n19k6/squarewave/v01_1000_rpm/oscilloscope_1.png

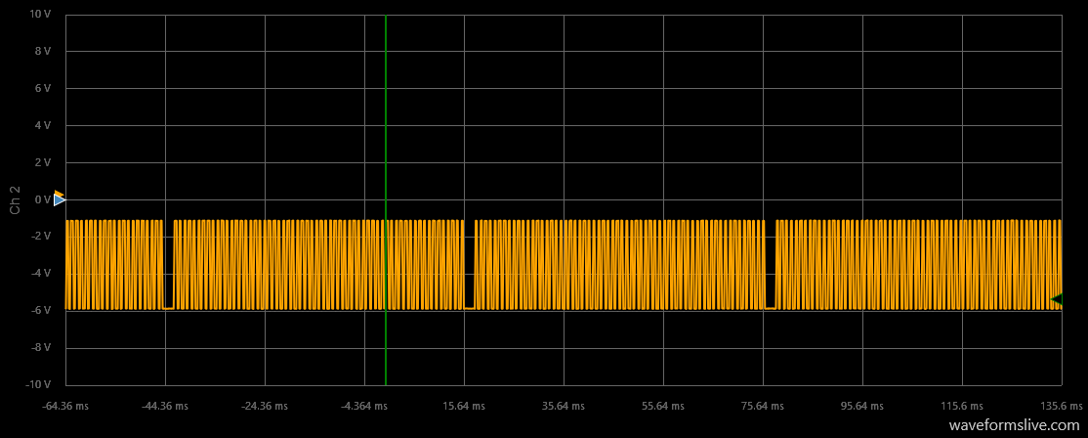
v01_1000_rpm/oscilloscope_1.png
