n19k6/squarewave/v02_maximum/az-logic-analyzer.jpg

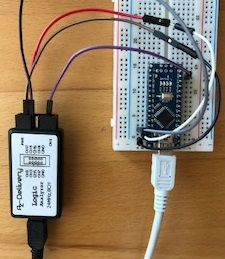
v02_maximum/az-logic-analyzer.jpg
