n19k6/squarewave/v02_maximum/signal.png

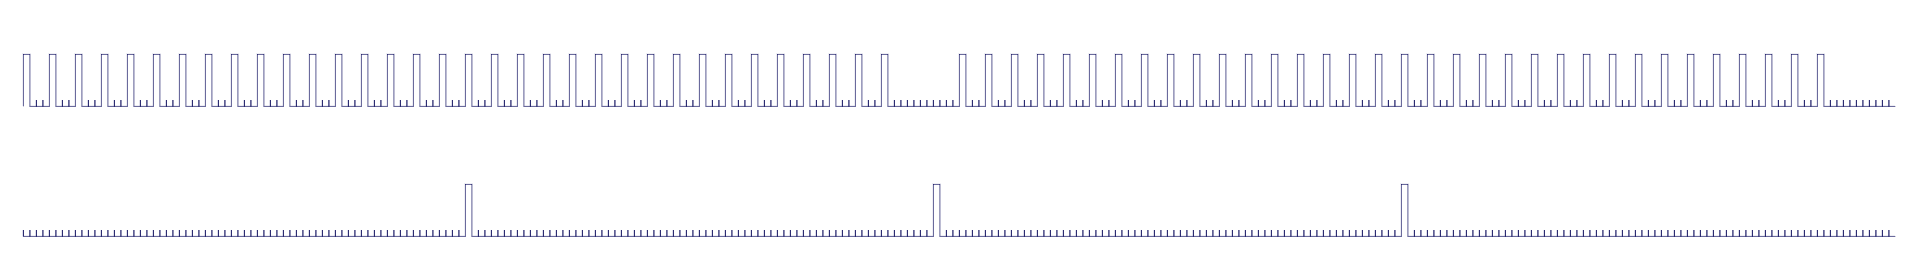
v02_maximum/signal.png
