n19k6/squarewave/v02_maximum/wave1.png

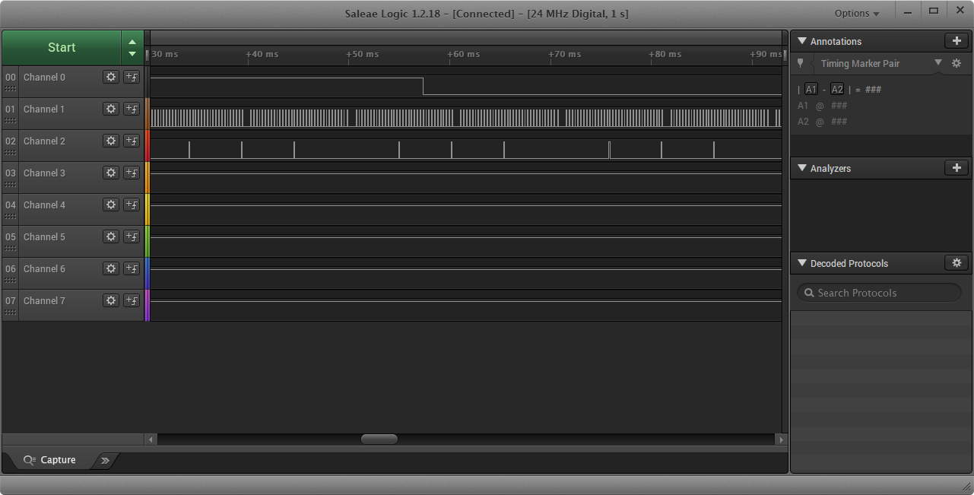
v02_maximum/wave1.png
