n19k6/squarewave/v02_maximum/wave2.png

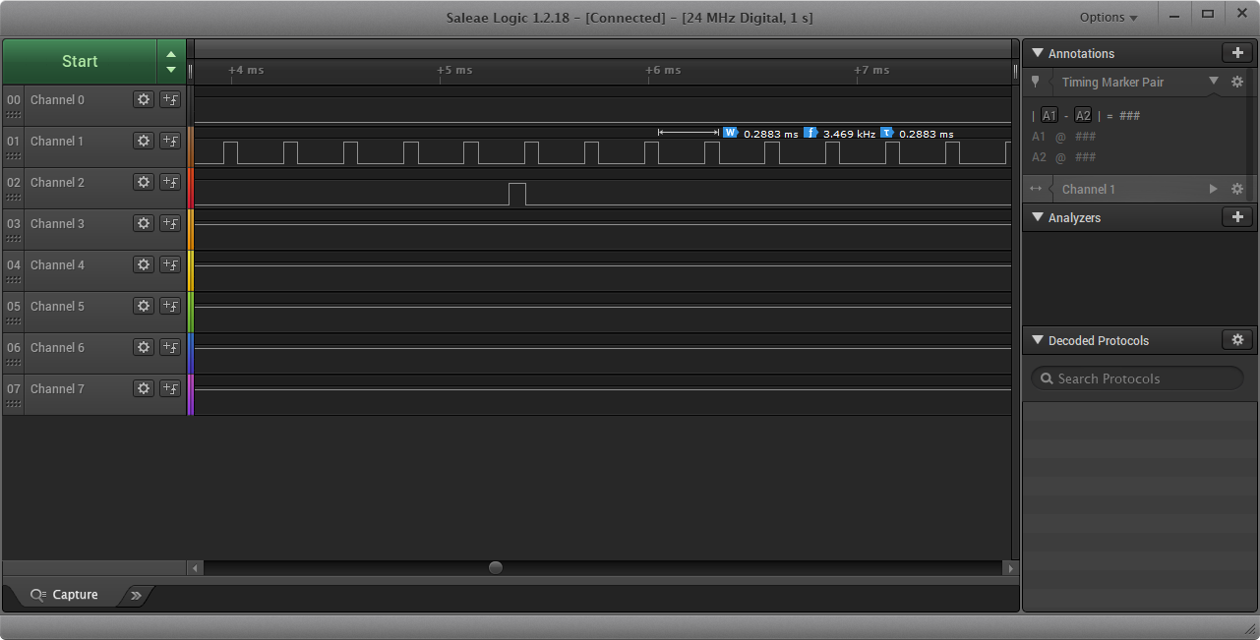
v02_maximum/wave2.png
