n19k6/squarewave/v04_sg/sketch_20210123a.png

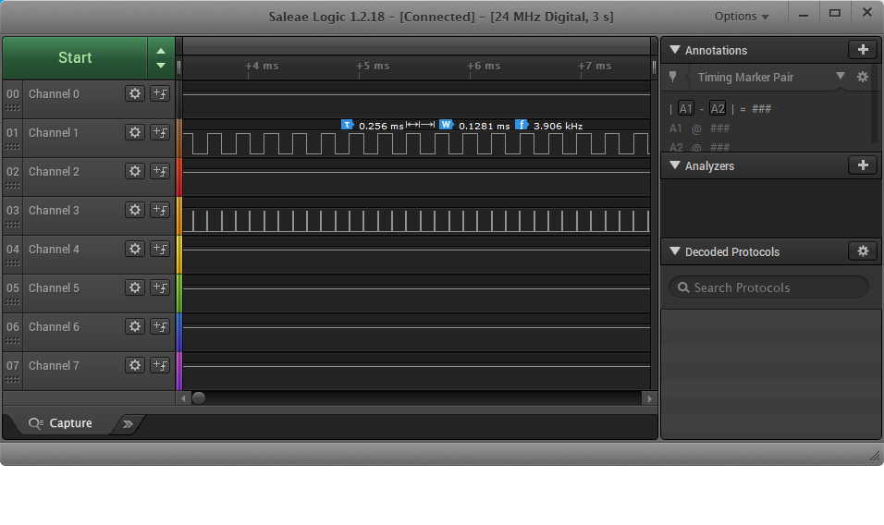
v04_sg/sketch_20210123a.png
