n19k6/squarewave/v04_sg/sketch_20210123d_100.png

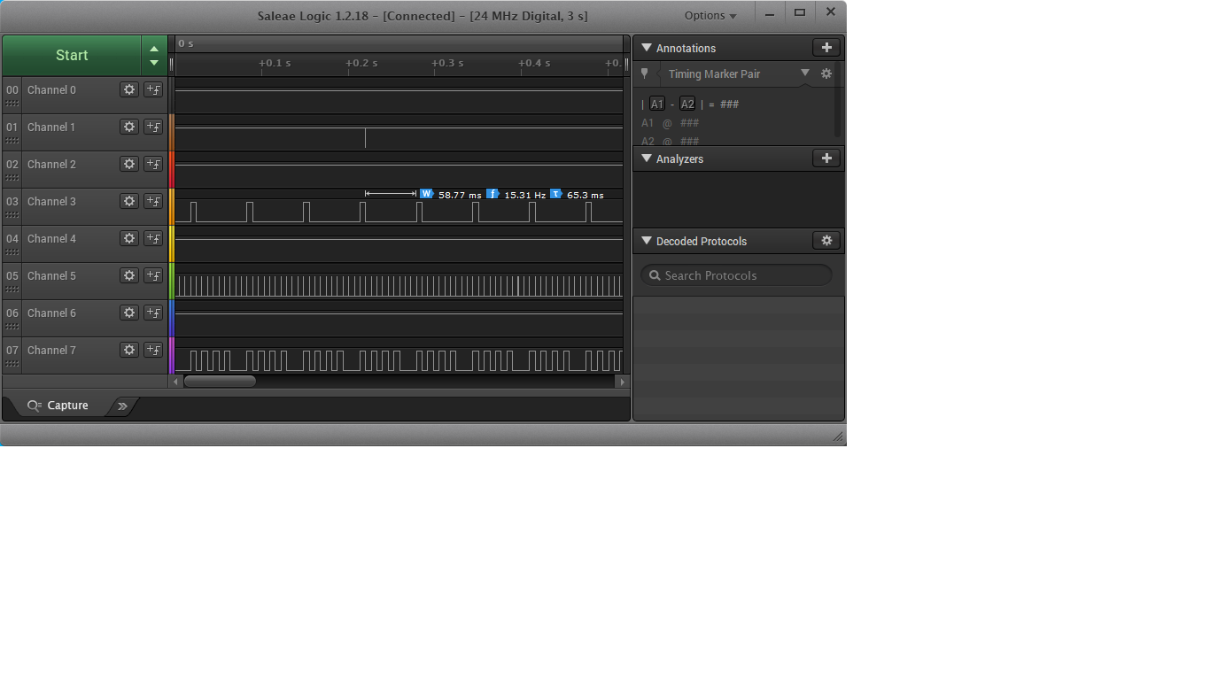
v04_sg/sketch_20210123d_100.png
