n19k6/squarewave/v04_sg/sketch_20210123f.png

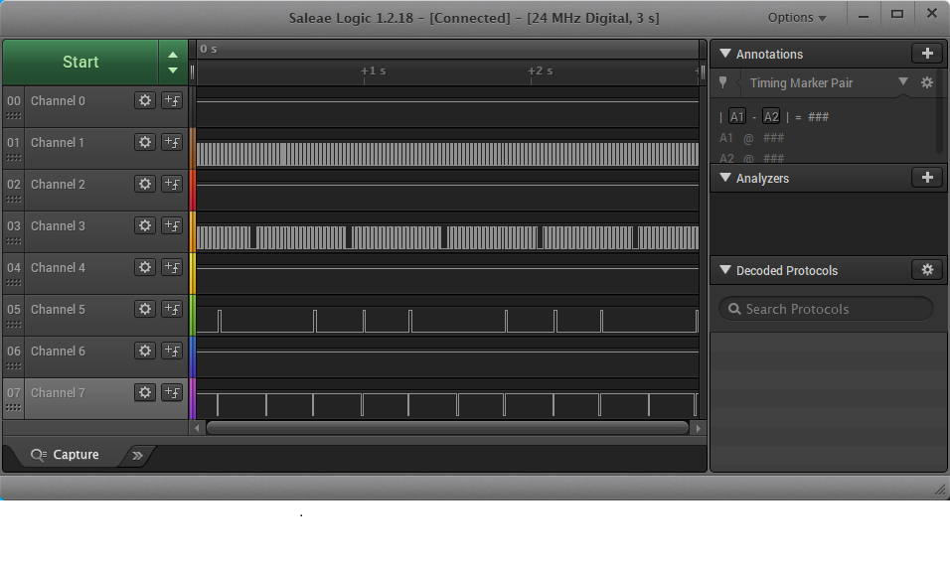
v04_sg/sketch_20210123f.png
