n19k6/squarewave/v04_sg/sketch_20210123g.png

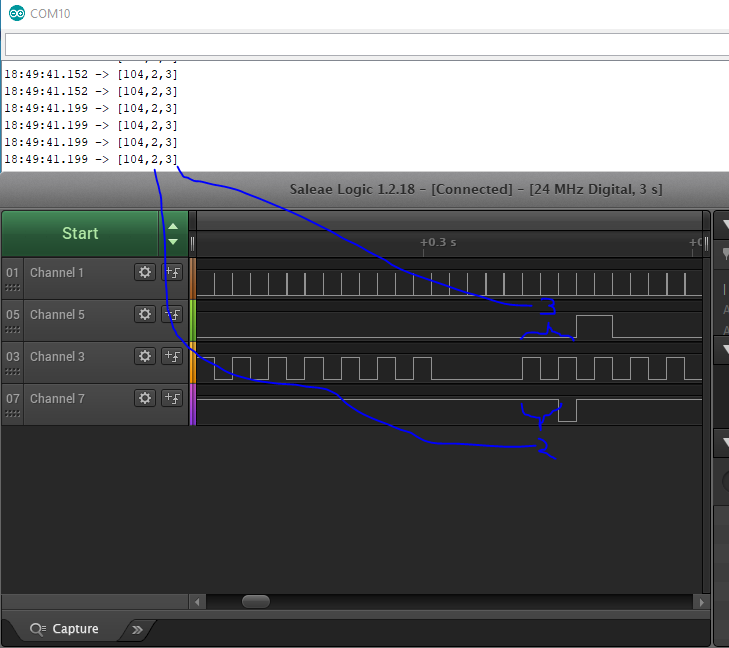
v04_sg/sketch_20210123g.png
