n19k6/squarewave/v04_sg/sketch_20210208a_timer2.png

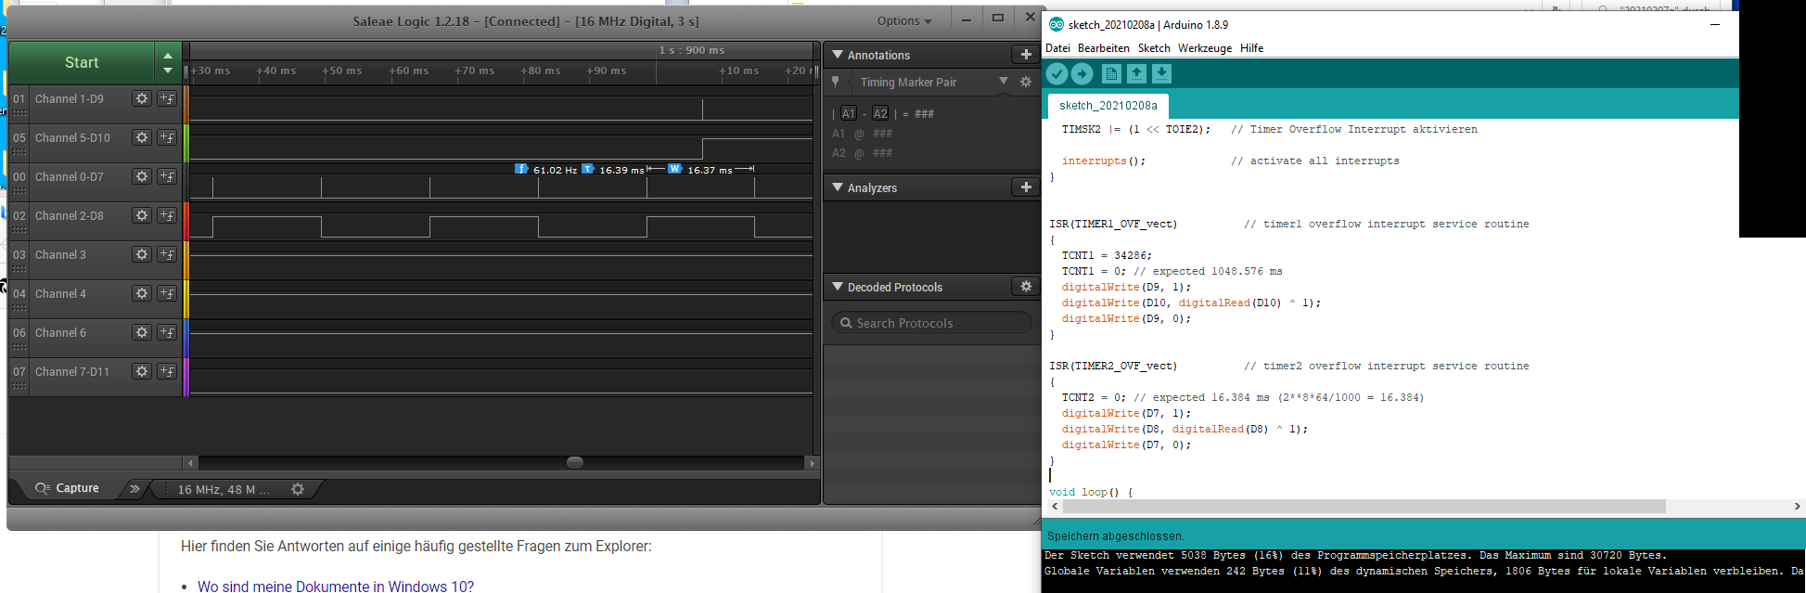
v04_sg/sketch_20210208a_timer2.png
