n19k6/squarewave/v04_sg/sketch_20210214b2.png

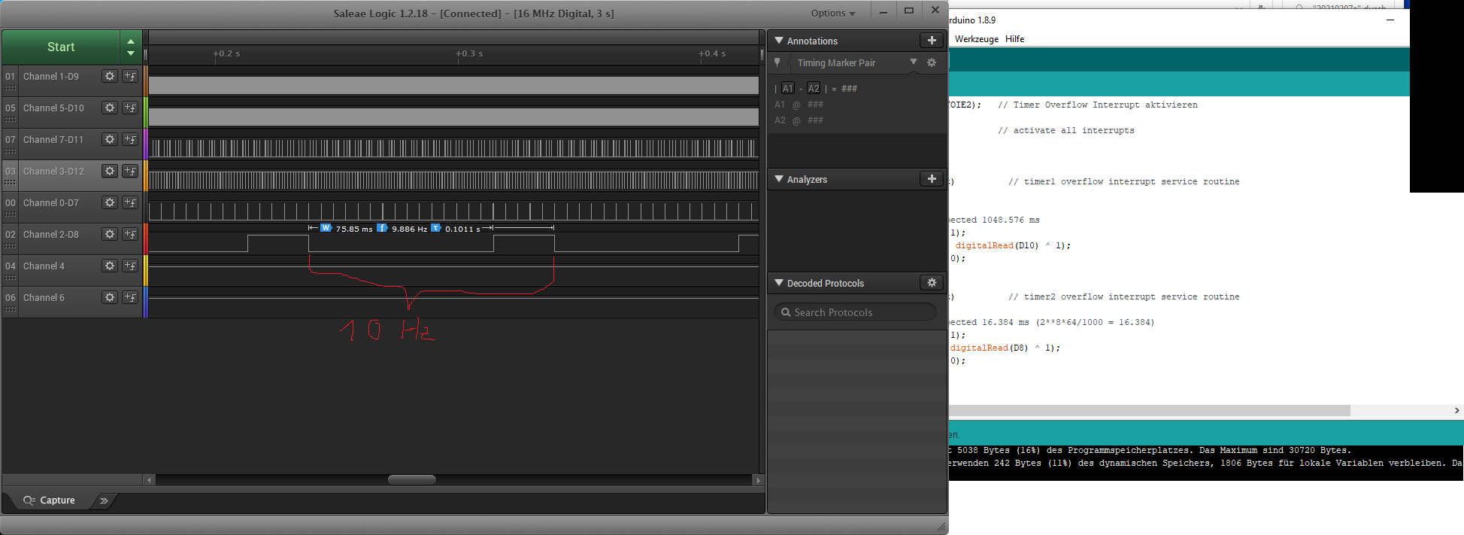
v04_sg/sketch_20210214b2.png
