n19k6/squarewave/v08_prototype_version_1/Pico_MCP3008_Schaltplan.png

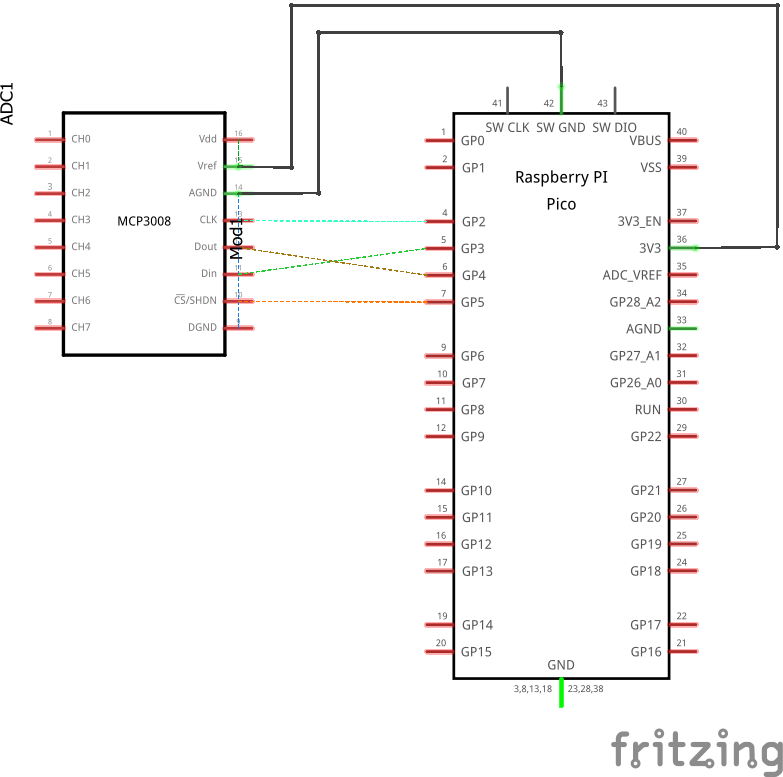
v08_prototype_version_1/Pico_MCP3008_Schaltplan.png
