n19k6/squarewave/v10_prototype_version_2/20220103/20210521_wegfahrsperre_002.png

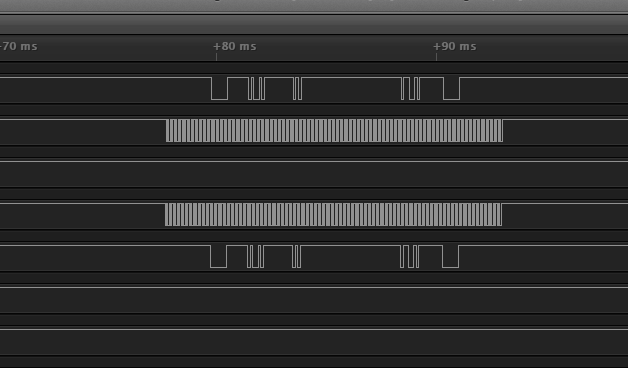
v10_prototype_version_2/20220103/20210521_wegfahrsperre_002.png
