n19k6/squarewave/v10_prototype_version_2/20220103/20220104_drei_signale_002a_freq_400_000.png

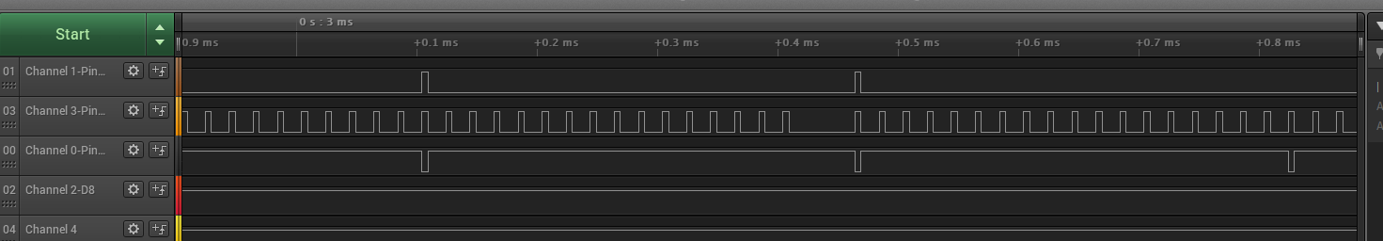
v10_prototype_version_2/20220103/20220104_drei_signale_002a_freq_400_000.png
