n19k6/squarewave/v10_prototype_version_2/20220103/20220104_drei_signale_003.png

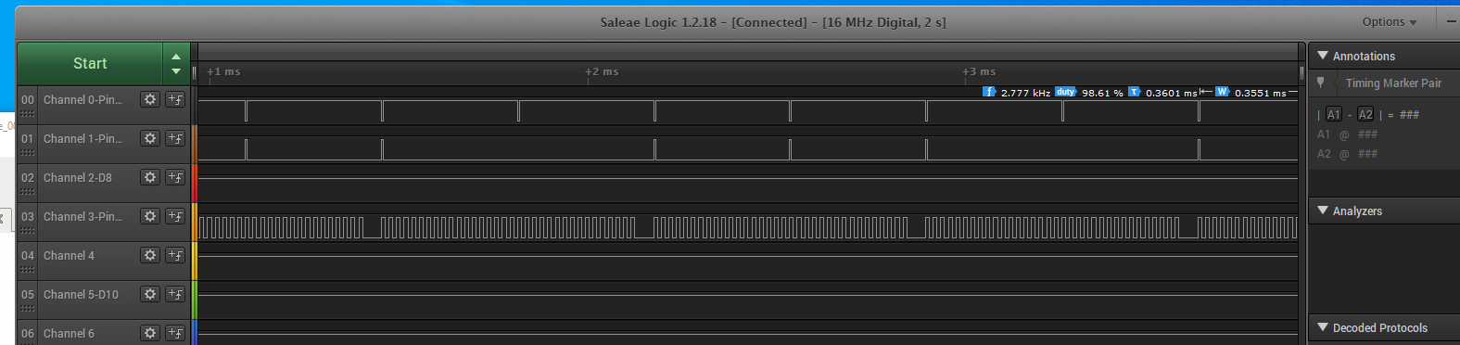
v10_prototype_version_2/20220103/20220104_drei_signale_003.png
