n19k6/squarewave/v11_honda_v1/01_input_docs/signal.png

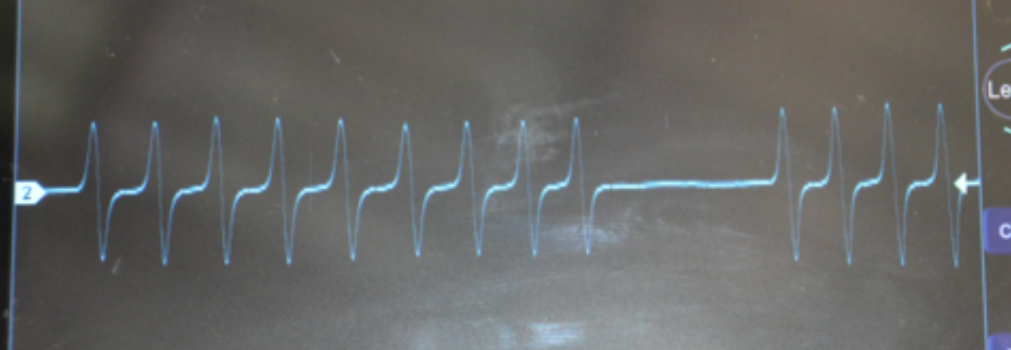
v11_honda_v1/01_input_docs/signal.png
