n19k6/squarewave/v11_honda_v1/01_input_docs/signal_max.png

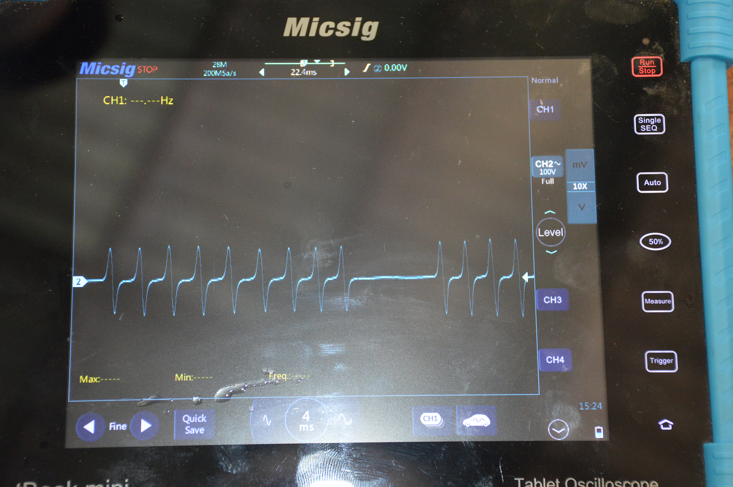
v11_honda_v1/01_input_docs/signal_max.png
