n19k6/squarewave/v01_measurement/oscilloscope.png

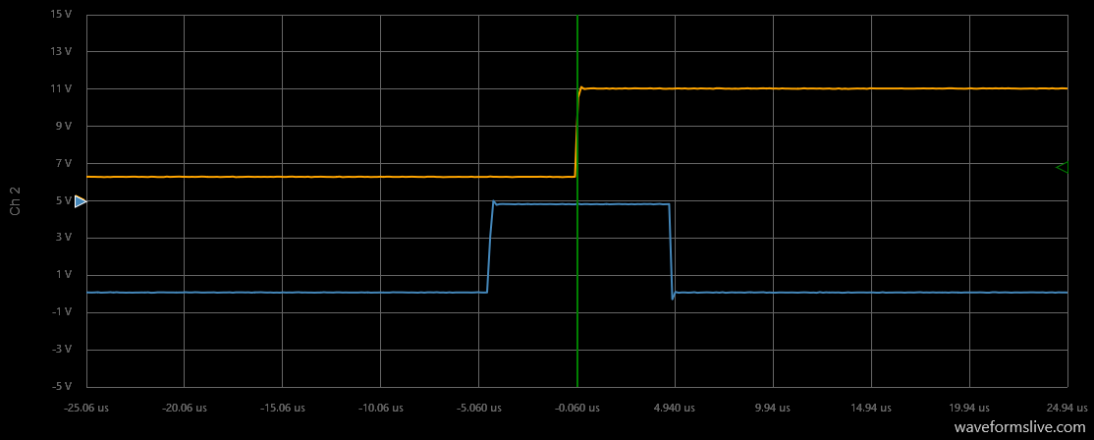
v01_measurement/oscilloscope.png
