n19k6/squarewave/v04_sg/sketch_20210123g_problem_val_a_2.png

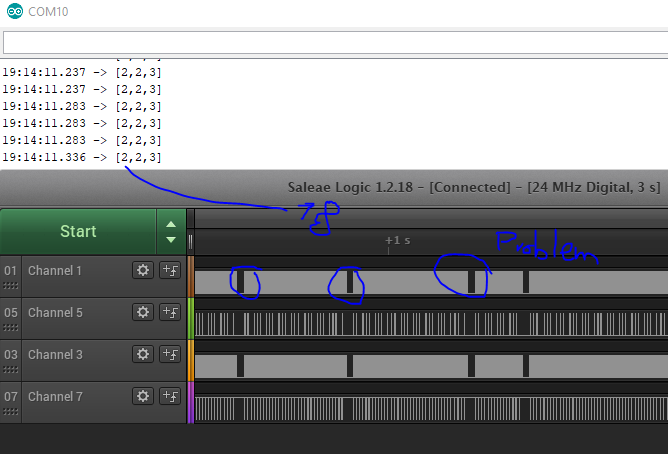
v04_sg/sketch_20210123g_problem_val_a_2.png
