n19k6/squarewave/v08_prototype_version_1/dump/exception1.py

# exception example
#import sys
from sys import exit
from time import sleep

try:
    print("a")
    #sleep(10)
    122/0
    exit(1)
    print("b")
except (SystemExit, KeyboardInterrupt):
    print("c")
