n19k6/squarewave/v01_ATtiny25_test/sketch_jul20e.ino

int analogPin = PB3; 
int val = 1;

volatile boolean buffer_PB0 = 0;
volatile boolean buffer_PB1 = 0;
volatile unsigned long timer1_count = 0;

void setup() {
  // put your setup code here, to run once:
  pinMode(PB0, OUTPUT);
  pinMode(PB1, OUTPUT);
  digitalWrite(PB1, LOW);
  // Timer 1
  noInterrupts();           // disable all interrupts temporarily
  TCCR1 = 0;
  TCCR1 |= (1 << CTC1);
  //TCCR1 |= (1 << CS10) | (1 << CS11) | (1 << CS13);
  //TCCR1 |= (1 << CS10) | (1 << CS13); //prescale 256
  TCCR1 |= (1 << CS11) | (1 << CS12); //prescale 32
  TCNT1 = 0;
  OCR1C = 255;
  TIMSK |= (1 << OCIE1A);
  interrupts();
  // Mehr Infos: https://arduino-projekte.webnode.at/registerprogrammierung/timer-interrupt/attiny/
}

ISR(TIMER1_COMPA_vect)        
{
  //TCNT0 = 0x80;
  //digitalWrite(PB1, 1);
  if (buffer_PB0) {
    digitalWrite(PB0, !buffer_PB0);
    buffer_PB0=!buffer_PB0;  
 // } else if (timer1_count % 4 == 1 && timer1_count != 5 && timer1_count != 9 && timer1_count != 5+36*4 && timer1_count != 9+36*4) {
 } else if (timer1_count % 2 == 1 && timer1_count != 3+36*2 && timer1_count != 5+36*2 && timer1_count != 144+3+36*2 && timer1_count != 144+5+36*2) {
    digitalWrite(PB0, !buffer_PB0);
    buffer_PB0=!buffer_PB0;   
  }
  if (buffer_PB1) {
    digitalWrite(PB1, !buffer_PB1);
    buffer_PB1=!buffer_PB1;  
 // } else if (timer1_count == 18*4 || timer1_count == 36*4 || timer1_count == 54*4) {
    } else if (timer1_count == 18*2 || timer1_count == 36*2 || timer1_count == 54*2 || timer1_count == 144+18*2 || timer1_count == 144+36*2 || timer1_count == 144+54*2 ) {
    digitalWrite(PB1, !buffer_PB1);
    buffer_PB1=!buffer_PB1;  
  }
  timer1_count++;
  if (timer1_count>288) {
    timer1_count=0;
  }
  //digitalWrite(PB1, 0);  
}

void loop() {
  val = analogRead(analogPin);
  if (val<10) {
    val=10;
  }
  OCR1C = val;
}
